SkiBikePrint/ERCF_Mods/Indignant_Elephant_Spool_Feed/Indignant Elephant.jpg

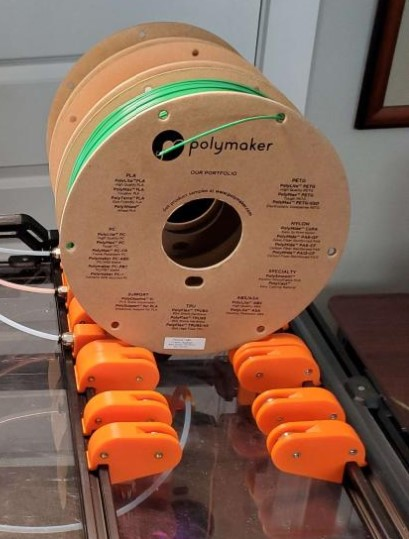
Indignant_Elephant_Spool_Feed/Indignant Elephant.jpg
