SkiBikePrint/ERCF_Mods/Carrot_Quiver_Buffer/3 Slot/Filament Slots(3) V2-300 x2.stl

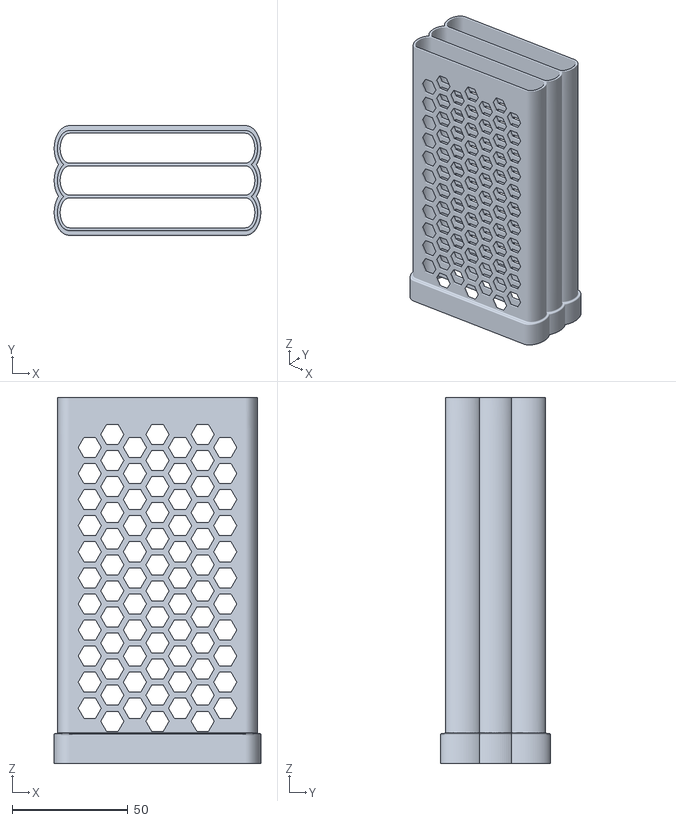
[picture p23: CAD file, 2024-01-08]
Carrot_Quiver_Buffer/3 Slot/Filament Slots(3) V2-300 x2.stl
89.2 x 47.4 x 158.0
