SkiBikePrint/ERCF_Mods/Carrot_Quiver_Buffer/4 SLot/Filament Slots(4) Lower.stl

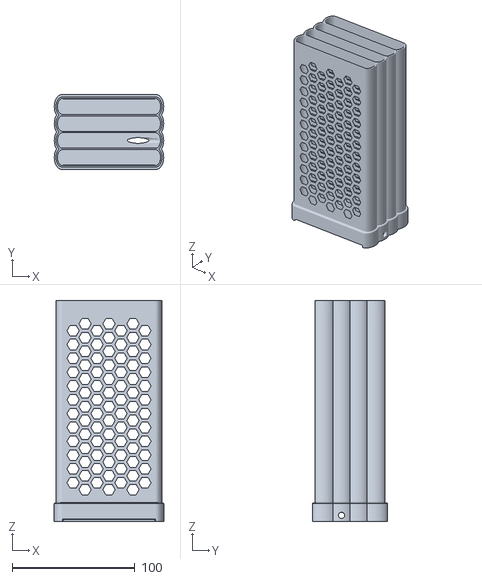
[picture p24: CAD file, 2024-01-08]
Carrot_Quiver_Buffer/4 SLot/Filament Slots(4) Lower.stl
89.2 x 61.2 x 180.0
