SkiBikePrint/ERCF_Mods/Indignant_Elephant_Spool_Feed/Bowden Mount.stl

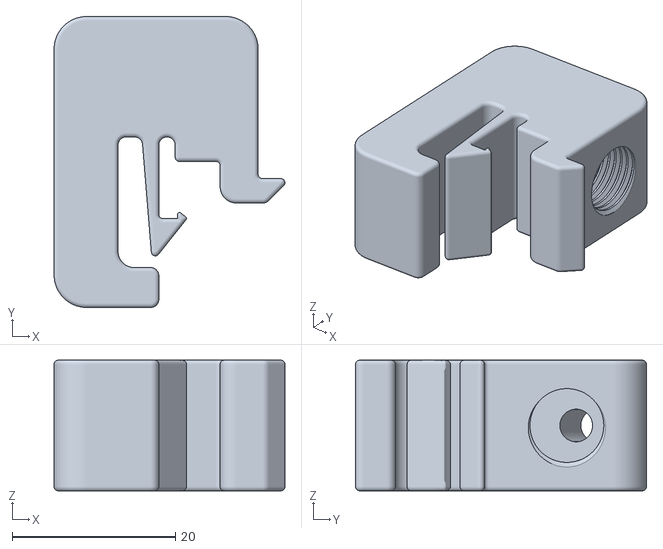
[picture p25: CAD file, 2022-11-13]
Indignant_Elephant_Spool_Feed/Bowden Mount.stl
28.3 x 35.6 x 16.0
