SkiBikePrint/ERCF_Mods/Trident SW Only Blobifier/stls/Arm Lower.stl

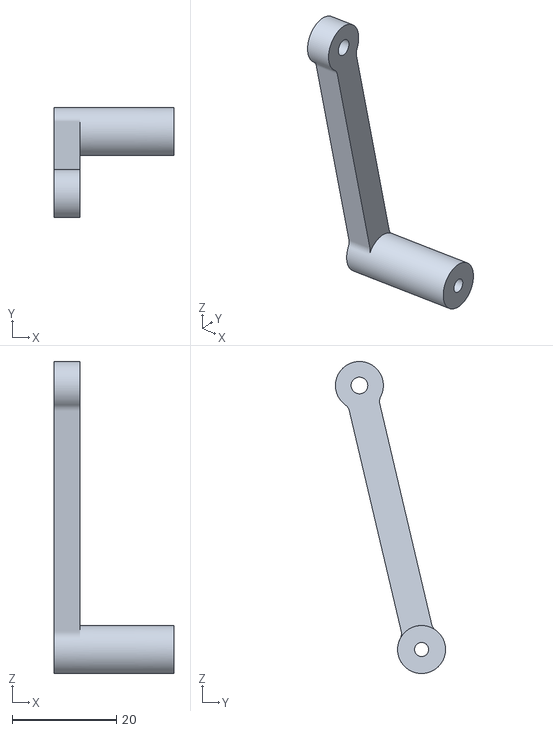
[picture p26: CAD file, 2024-03-15]
Trident SW Only Blobifier/stls/Arm Lower.stl
23.0 x 21.1 x 59.8
