SkiBikePrint/ERCF_Mods/Carrot_Quiver_Buffer/3 Slot/Top Mount.stl

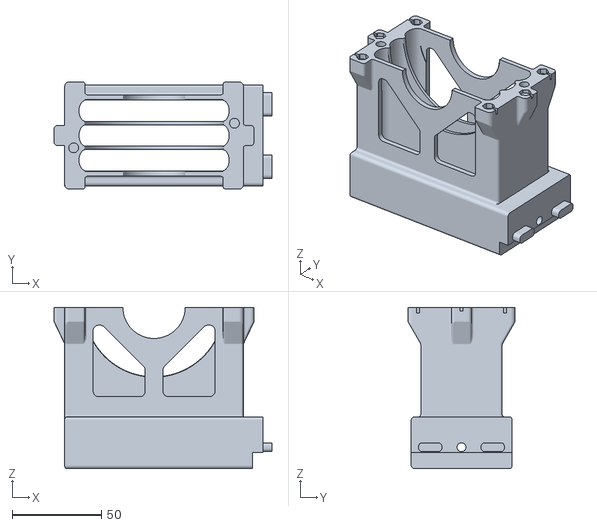
[picture p27: CAD file, 2024-01-07]
Carrot_Quiver_Buffer/3 Slot/Top Mount.stl
122.0 x 60.0 x 90.3
