SkiBikePrint/ERCF_Mods/Carrot_Quiver_Buffer/4 SLot/Wheel Block.stl

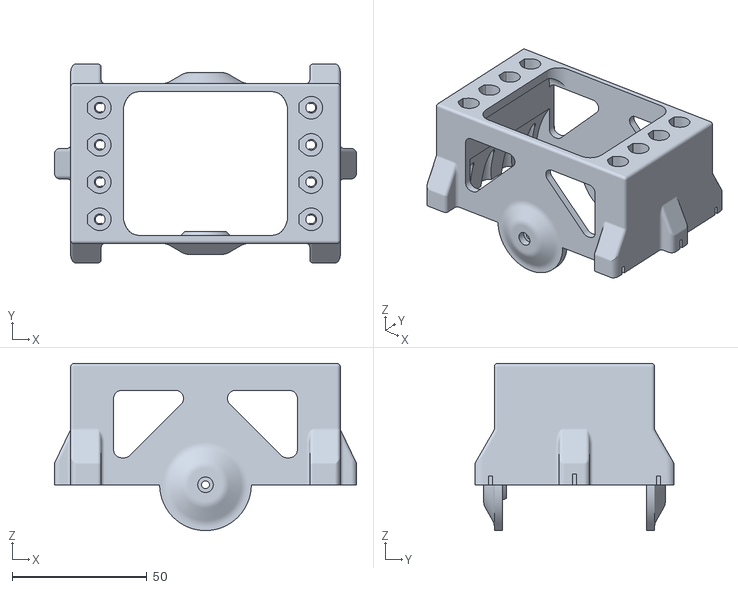
[picture p28: CAD file, 2024-01-07]
Carrot_Quiver_Buffer/4 SLot/Wheel Block.stl
112.0 x 73.8 x 62.0
