SkiBikePrint/ERCF_Mods/Trident SW Only Blobifier/stls/Arm Upper.stl

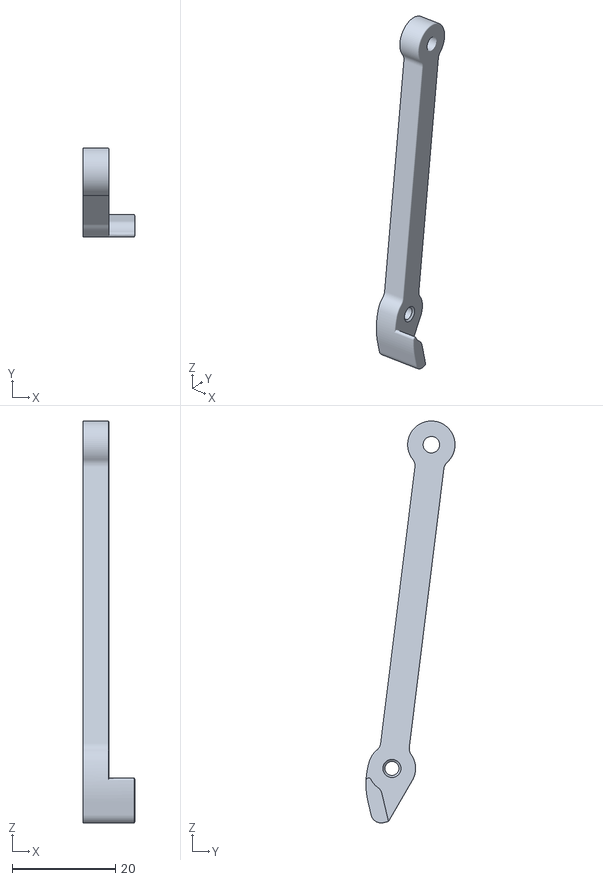
[picture p29: CAD file, 2024-03-15]
Trident SW Only Blobifier/stls/Arm Upper.stl
10.0 x 17.3 x 78.0
