SkiBikePrint/ERCF_Mods/Carrot_Quiver_Buffer/3 Slot/Wheel Block.stl

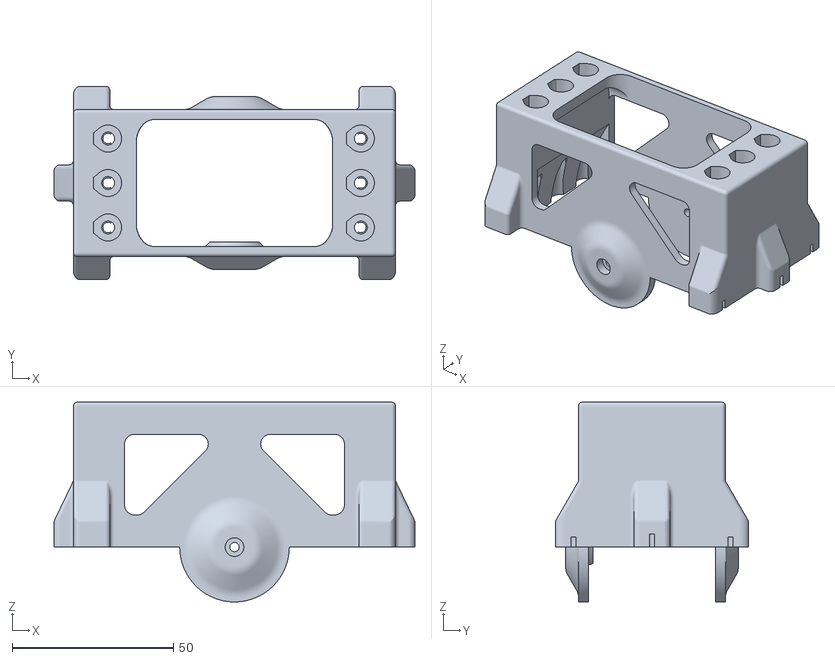
[picture p30: CAD file, 2024-01-07]
Carrot_Quiver_Buffer/3 Slot/Wheel Block.stl
112.0 x 60.0 x 62.0
