SkiBikePrint/ERCF_Mods/Carrot_Quiver_Buffer/4 SLot/Axle.stl

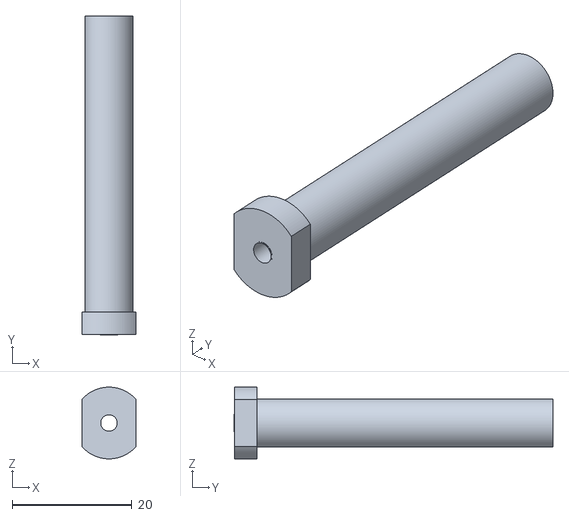
[picture p31: CAD file, 2024-01-07]
Carrot_Quiver_Buffer/4 SLot/Axle.stl
9.00 x 53.4 x 12.0
