SkiBikePrint/ERCF_Mods/Trident SW Only Blobifier/stls/Blob Bucket 300.stl

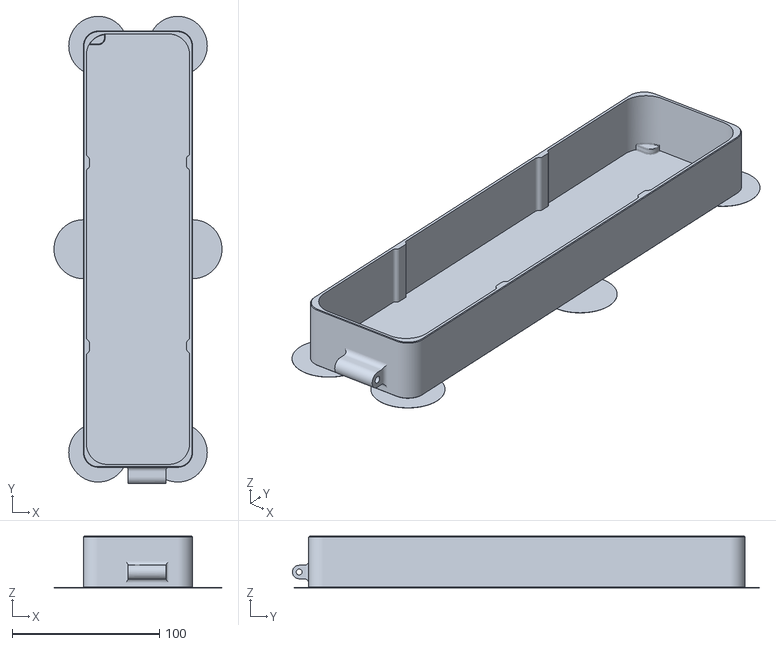
[picture p32: CAD file, 2024-03-15]
Trident SW Only Blobifier/stls/Blob Bucket 300.stl
114.0 x 317.1 x 35.0
