SkiBikePrint/ERCF_Mods/Carrot_Quiver_Buffer/3 Slot/Axle.stl

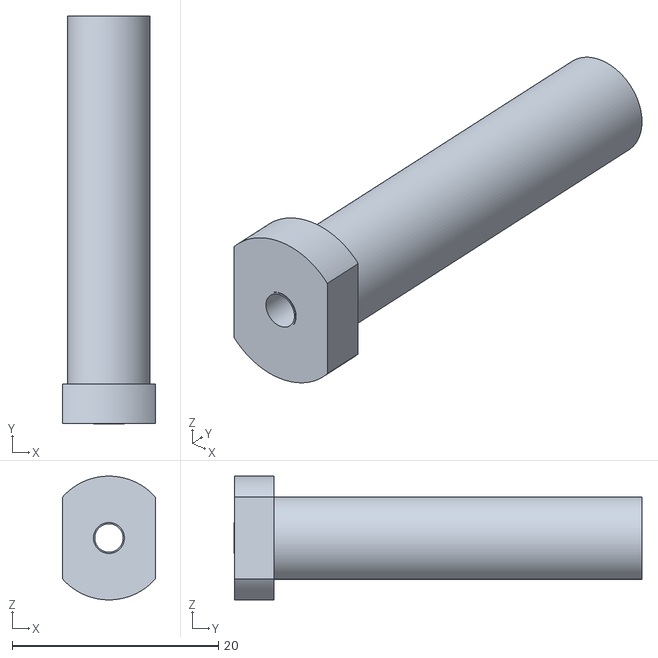
[picture p33: CAD file, 2024-01-07]
Carrot_Quiver_Buffer/3 Slot/Axle.stl
9.00 x 39.6 x 12.0
