SkiBikePrint/ERCF_Mods/Carrot_Quiver_Buffer/4 SLot/Bottom Block.stl

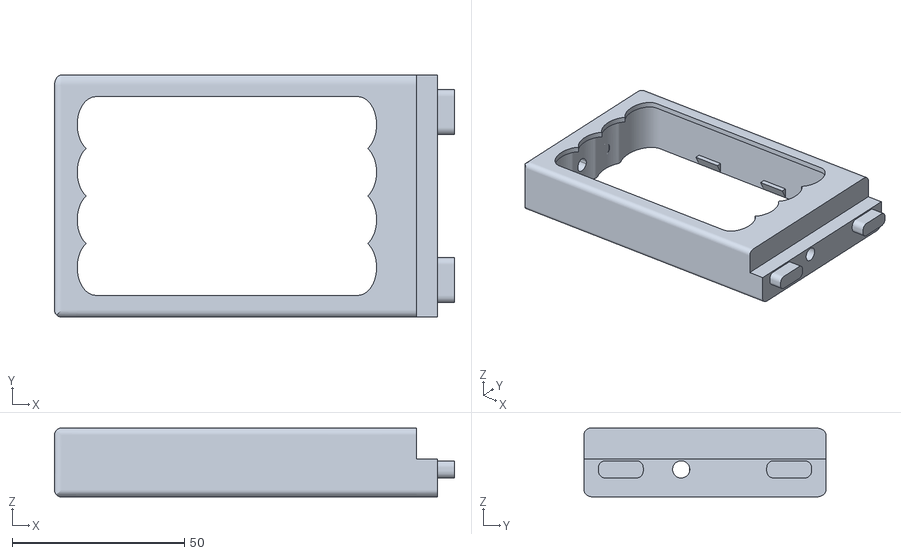
[picture p34: CAD file, 2024-01-07]
Carrot_Quiver_Buffer/4 SLot/Bottom Block.stl
116.0 x 70.2 x 20.0
