SkiBikePrint/ERCF_Mods/Carrot_Quiver_Buffer/3 Slot/Bottom Block.stl

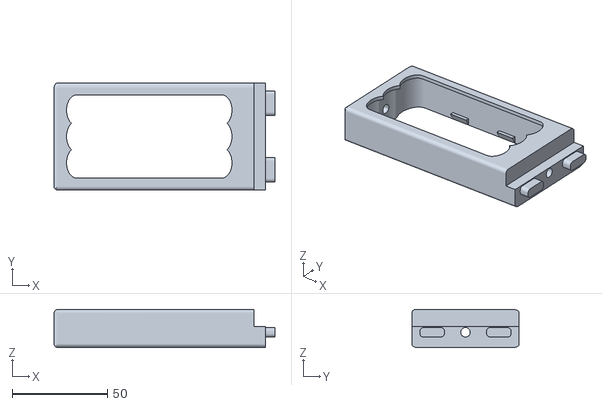
[picture p35: CAD file, 2024-01-07]
Carrot_Quiver_Buffer/3 Slot/Bottom Block.stl
116.0 x 56.4 x 20.0
