SkiBikePrint/ERCF_Mods/Carrot_Quiver_Buffer/4 SLot/Top Mount.stl

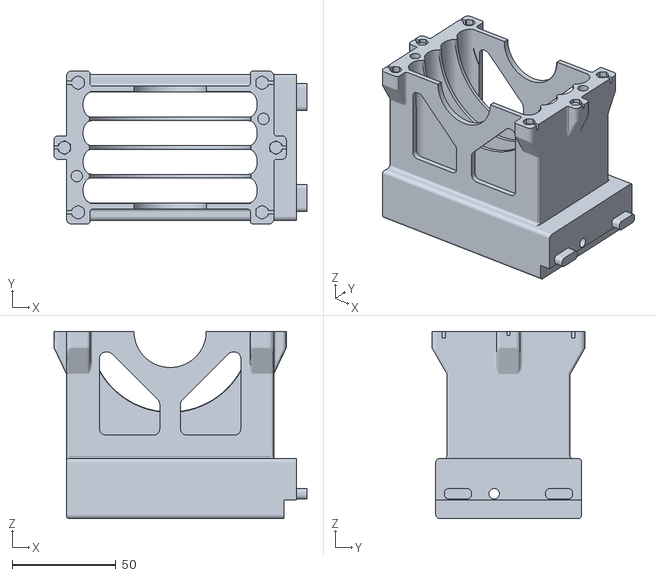
[picture p36: CAD file, 2024-01-07]
Carrot_Quiver_Buffer/4 SLot/Top Mount.stl
122.0 x 73.8 x 90.3
