SkiBikePrint/ERCF_Mods/Carrot_Quiver_Buffer/3 Slot/Filament Slots(3) Trident x2.stl

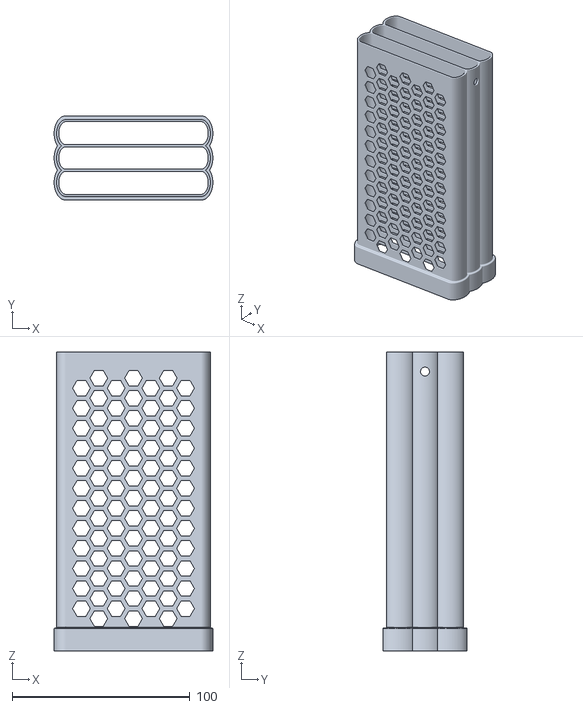
[picture p37: CAD file, 2024-01-07]
Carrot_Quiver_Buffer/3 Slot/Filament Slots(3) Trident x2.stl
89.2 x 47.4 x 168.0
