SkiBikePrint/ERCF_Mods/Carrot_Quiver_Buffer/4 SLot/Filament Slots(4) x2 Trident.stl

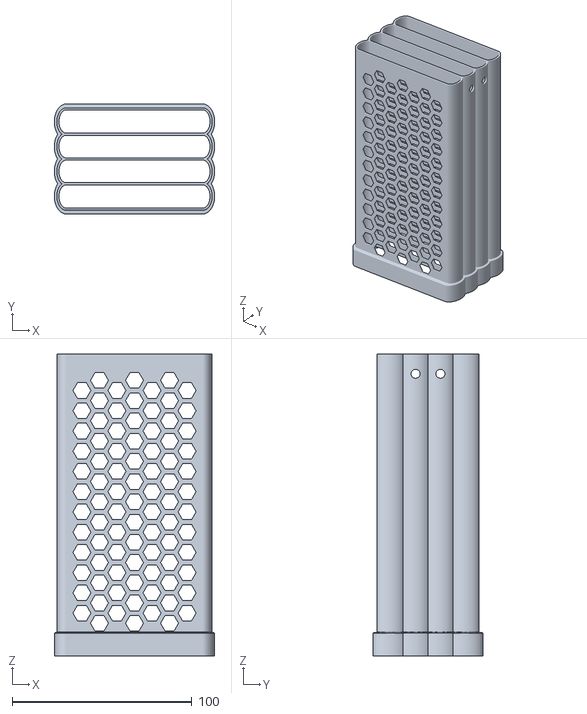
[picture p38: CAD file, 2024-01-07]
Carrot_Quiver_Buffer/4 SLot/Filament Slots(4) x2 Trident.stl
89.2 x 61.2 x 168.0
