SkiBikePrint/ERCF_Mods/Carrot_Quiver_Buffer/3 Slot/Axle Spacer.stl

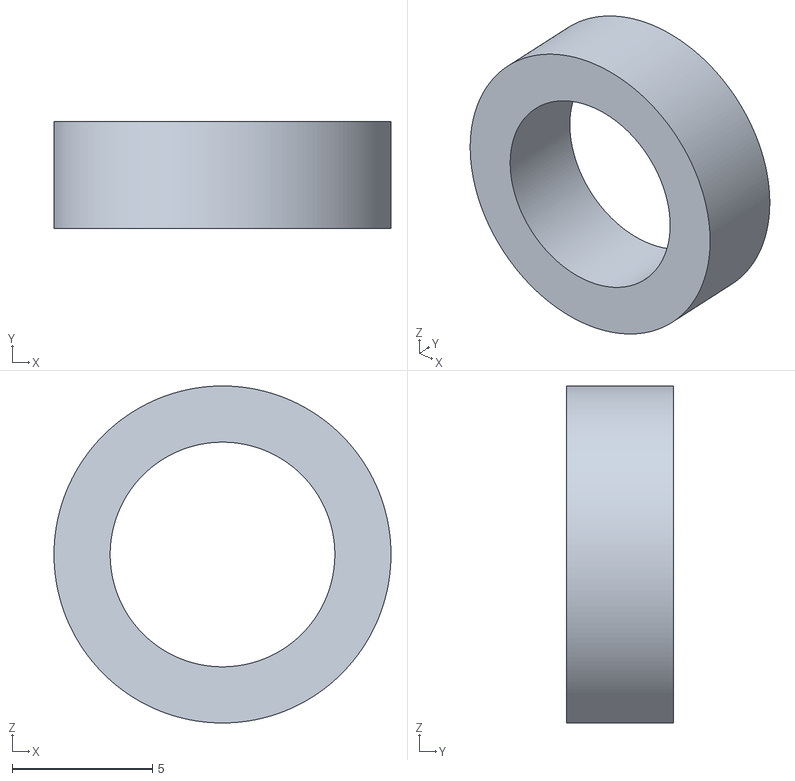
[picture p39: CAD file, 2024-01-07]
Carrot_Quiver_Buffer/3 Slot/Axle Spacer.stl
12.0 x 3.82 x 12.0
